slackDSP/slackDSP_mini/firmware/slackdsp_mini.c

/*
 *File:   slackdsp_mini.c
 *
 *   Copyright © 2015 Ian Maltby
 * This work is free. You can redistribute it and/or modify it under the
 * terms of the Do What The Fuck You Want To Public License, Version 2,
 * as published by Sam Hocevar. See the COPYING file for more details.
 */

#include <xc.h>
#include <stdio.h>
#include <stdlib.h>
#include "slackdsp_mini.h"
#include "sram.h"

//sine wavetable
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


//delayline

int delayline(long d_length, long d_time, int d_mod, int d_in) {

    static long writeaddress;
    static long readaddress;
    int d_out;

    writeaddress = (writeaddress + 2) & (d_length - 1);
    readaddress = (writeaddress + d_length - d_time + d_mod) & (d_length - 2);
    sram_write(writeaddress, d_in);
    d_out = sram_read(readaddress);
    return (d_out);
}


//mulx

int mulx(int m_in1, int m_in2) {

    long sample32;

    sample32 = m_in1 * (long) m_in2;

    return (sample32 >> 15);

}

//add

int add(int a_in1, int a_in2) {

    long sample32;

    sample32 = a_in1 + (long) a_in2;
    if (sample32 < -32768)
        sample32 = -32768;
    if (sample32 > 32767)
        sample32 = 32767;

    return (sample32);

}

//clipper

int clip(int c_level, int c_in) {

    if (c_in < -c_level)
        c_in = -c_level;
    if (c_in > c_level)
        c_in = c_level;

    return (c_in);
}


//pitchshifter

int pitchshift(int s_shift, int s_in) {

#define slength 2048

    static int buffer[slength];
    static int writeaddress;
    static int readaddress;
    long sample1;
    long sample2;
    int env;
    static long counter;

    writeaddress = (writeaddress + 1) & (slength - 1);
    buffer[writeaddress] = s_in;

    counter = counter + s_shift;
    if (counter > 32767) {
        counter = counter & 32767;
        readaddress = (readaddress + 2) & (slength - 1);
    }

    env = (writeaddress - readaddress) << 5;
    if (env < 0)
        env = ~env;

    sample1 = buffer[readaddress];
    sample2 = buffer[((readaddress + (slength / 2)) & (slength - 1))];
    sample1 = (sample1 * env);
    sample2 = (sample2 * (32767 - env));

    return ((sample1 + sample2) >> 15);
}

//lowpass filter

int lowpass(int lp_freq, int lp_in) {

    static long lp_out = 0;

    lp_out = ((((lp_in - lp_out) * lp_freq) >> 15) + lp_out);

    return (lp_out);
}

//highpass filter

int hipass(int hp_freq, int hp_in) {

    int hp_out;
    static long h_lp = 0;

    hp_out = ((((hp_in - h_lp) * hp_freq) >> 15) + h_lp) - hp_in;

    return (hp_out);

}
//VCO

int vco(long v_speed) {

    static long counter = 0;

    counter = (counter + v_speed) & 32767;

    return (sine[counter >> 7]);

}

//random number generator

int random(void) {
    static long lfsr = 1234;
    int xorbit;
#define bit1 28
#define bit2 31
    xorbit = ((lfsr >> (bit1 - 1) ^ (lfsr >> (bit2 - 1)))) & 1;
    lfsr = (lfsr << 1 | xorbit);
    return (lfsr);
}

//crossfade two signals

int crossfade(int cf_ctrl, int in_1, int in_2) {

    long sample32;

    sample32 = ~in_1 + (long) in_2;
    sample32 = (cf_ctrl * sample32) >> 15;
    sample32 = sample32 + in_1;

    return (sample32);

}

//gain and clipper

int gain(int g_level, int gc_level, int g_in) {

    long sample32;

    sample32 = (g_level >> 5) * (long) g_in;

    if (sample32 < -gc_level)
        sample32 = -gc_level;
    if (sample32 > gc_level)
        sample32 = gc_level;

    return (sample32);
}

int pitchshift2(int s_shift, int s_in) {

#define slength2 2048

    static int buffer2[slength2];
    static int writeaddress2;
    static int readaddress2;
    long sample1;
    long sample2;
    int env;
    static long counter2;

    writeaddress2 = (writeaddress2 + 1) & (slength2 - 1);
    buffer2[writeaddress2] = s_in;

    counter2 = counter2 + s_shift;
    if (counter2 > 32767) {
        counter2 = counter2 & 32767;
        readaddress2 = (readaddress2 + 2) & (slength2 - 1);
    }

    env = (writeaddress2 - readaddress2) << 5;
    if (env < 0)
        env = ~env;

    sample1 = buffer2[readaddress2];
    sample2 = buffer2[((readaddress2 + (slength2 / 2)) & (slength2 - 1))];
    sample1 = (sample1 * env);
    sample2 = (sample2 * (32767 - env));

    return ((sample1 + sample2) >> 15);
}

//Semitone

int semitones(int st_in) {

    return (semitone_table[st_in]);
}

//Saw LFO

int saw_lfo(int saw_speed) {

    static long saw_counter = 0;
    static int saw_out = 0;

    saw_counter = saw_counter + saw_speed;
    if (saw_counter > 32767) {
        saw_counter = saw_counter & 32767;
        saw_out = (saw_out + 32) & 32767;
    }
    return (saw_out);

}

//Tri LFO

int tri_lfo(int tri_speed) {

    static long tri_counter = 0;
    static long tri = 0;
    int tri_out = 0;

    tri_counter = tri_counter + tri_speed;
    if (tri_counter > 32767) {
        tri_counter = tri_counter & 32767;
        tri = (tri + 64) & 65535;
    }
    tri_out = tri - 32767;
    if (tri_out < 0)
        tri_out = ~tri_out;

    return (tri_out);

}

int logpot(int logpot_in) {

    return (log_pot_scale[logpot_in >> 7]);

}

//State Variable Filter
//http://www.musicdsp.org/showArchiveComment.php?ArchiveID=142

int svf(int svf_freq, int svf_q, int svf_type, int svf_in) {

    static long low = 0;
    static long band = 0;
    long high;

    low = low + ((svf_freq * band) >> 15);
    high = svf_in - low - ((svf_q * band) >> 15);
    band = ((svf_freq * high) >> 15) + band;

    if (band < -32767)
        band = -32767;
    if (band > 32767)
        band = 32767;

    if (svf_type == bp)
        return (band);

    if (svf_type == hp)
        return (high);

    else

        return (low);

}

//reverse delayline

int revdelay(long rd_length, long rd_time, int rd_in) {

    static long rdwriteaddress = 0;
    static long rdreadaddress = 0;
    int rd_out;

    rdwriteaddress = (rdwriteaddress + 2);
    if (rdwriteaddress > rd_time)
        rdwriteaddress = 0;

    rdreadaddress = (rdreadaddress - 2);
    if (rdreadaddress < 0)
        rdreadaddress = rd_time;

    sram_write(rdwriteaddress, rd_in);
    rd_out = sram_read(rdreadaddress);
    return (rd_out);
}

//blend

int blend(int b_ctrl, int b_in_1, int b_in_2) {

    long sample32;
    long ctrl1;
    long ctrl2;

    ctrl2 = b_ctrl;
    if (ctrl2 > 16383)
        ctrl2 = 16383;

    ctrl1 = ~b_ctrl;
    if (ctrl1 > -16383)
        ctrl1 = 16383;
    else
        ctrl1 = ctrl1 + 32767;

    sample32 = (ctrl1 * b_in_1) + (ctrl2 * b_in_2);

    return (sample32 >> 14);

}

//Random LFO

int random_lfo(int random_speed) {

    static long random_counter = 0;
    static int random_out = 0;

    random_counter = random_counter + random_speed;
    if (random_counter > 33554431) {
        random_counter = random_counter & 33554431;
        random_out = rand();

    }
    return (random_out);

}

//envelope follower
//http://www.musicdsp.org/archive.php?classid=0#136

int envelope(int env_attack, int env_release, int env_in) {

    static long env_out = 0;
    int temp;

    temp = abs(env_in);

    if (env_out < temp)
        env_out = temp + ((env_attack * (env_out - temp)) >> 15);

    else

        env_out = temp + ((env_release * (env_out - temp)) >> 15);

    return (env_out);

}

//hyper_tri LFO

int hyper_tri_lfo(long hpt_speed) {

    static long hpt_counter = 0;
    static int pos = 0;

    hpt_counter = hpt_counter + hpt_speed;
    if (hpt_counter > 32767) {
        hpt_counter = hpt_counter & 32767;
        pos = (pos + 1) & 1023;

    }

    return (hypertri[pos]);
}

//serial_send - sends a 16 bit int to the serial port

void serial_send(int s_out, int s_delay) {

    static int serial_delay = 0;

    serial_delay = serial_delay + 1;

    if (serial_delay >= s_delay) {
        serial_delay = 0;
        U1TXREG = s_out >> 8;
        U1TXREG = s_out;

    }
}
